Wohnmobil-Display/Wohnmobil-Display/bilder/screenshots/allgemein.png

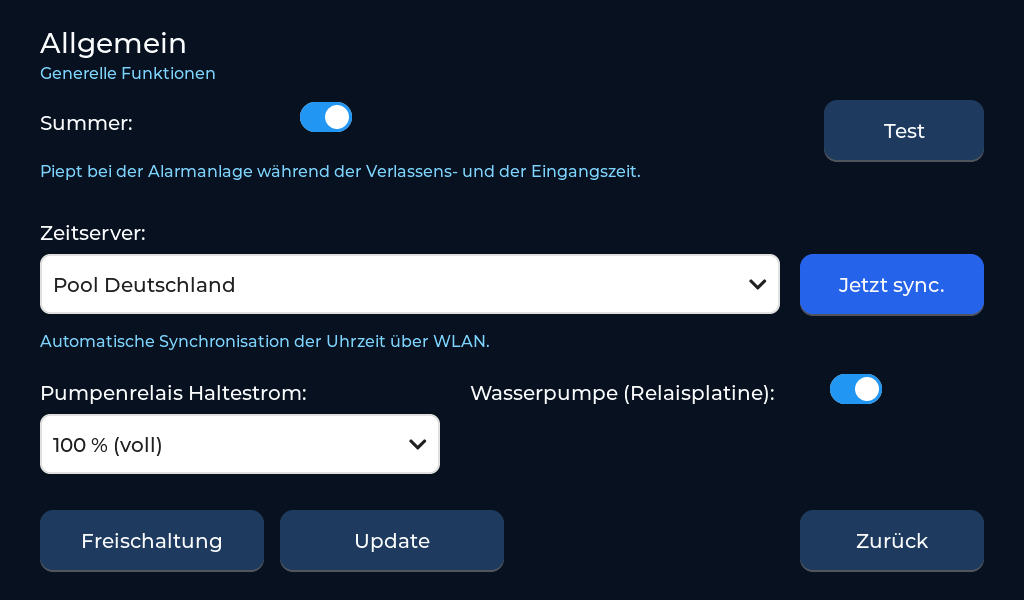
bilder/screenshots/allgemein.png
